AL-FC/AL-FanControl/arduino/bridgehead5V_ino/bridgehead5V_ino.ino

// fancontrol.ino
//
// Intentionally left simple and stupid so that all intelligent code can reside on the host side.

#include <SoftPWM.h>

// pins to which the fans are connected physically
// connector index  0  1  2  3   4   5   6   7
int PINS_PWM[]   = {2, 6}; //, 9, 4, A3, 15, 10, A1};
int PINS_PULSE[] = {3, 7}; //, 8, 5, A2, 14, 16, A0};

void setup() {
  // initialize serial connection
  Serial.begin(9600);
  
  // init pwm
  SoftPWMBegin();
  for (int i = 0; i < 2; i++) {      
    pinMode(PINS_PULSE[i], INPUT);
    digitalWrite(PINS_PULSE[i],HIGH);
    
    SoftPWMSetFadeTime(PINS_PWM[i], 0, 0);
    SoftPWMSet(PINS_PWM[i], 0);
  }
}

void loop() {
  // get message from serial console
  String message = "";
  while (Serial.available())
    message.concat((char) Serial.read());
  if (message == "")
    return;

  // iterate fans, collect pulse durations
  String pulseDurations = ":";
  for (int i = 0; i < 2; i++) {
    // parse value left of a ';' 
    int value = message.substring(0, message.indexOf(';')).toInt();
    
    SoftPWMSet(PINS_PWM[i], value);
    
    // strip part left of a ';' from message
    message = message.substring(message.indexOf(';') + 1);

    // respond with pulse durations
    pulseDurations = pulseDurations + String(pulseIn(PINS_PULSE[i], LOW)) + ";";
    
    // if there is no further ';' in the message, parse and set the rest of it
    if (message.indexOf(';') == -1)
      SoftPWMSet(PINS_PWM[i], message.toInt());
  }
  Serial.println(pulseDurations);
}
