AL-FC/AL-FanControl/python/fancontrol/learn.py

'''
Learns the correlations between the fans and the temps.
'''
from __future__ import (absolute_import, division, print_function,
                        unicode_literals)


def main():
    '''
    Put system under load and determine minimum viable fan speeds.
    Log fan speeds and temperatures, calculate correlations.
    '''
    pass
