AL-FC/AL-FanControl/arduino/blink_isr/sketch_jan23d/sketch_jan23d.ino

/* Arduino 101: timer and interrupts
   1: Timer1 compare match interrupt example 
   more infos: http://www.letmakerobots.com/node/28278
   created by RobotFreak 
*/

#define ledPin 17

void setup()
{
  pinMode(ledPin, OUTPUT);
  
  // initialize timer1 
  noInterrupts();           // disable all interrupts
  TCCR1A = 0;
  TCCR1B = 0;
  TCNT1  = 0;

  OCR1A = 31250;            // compare match register 16MHz/256/2Hz
  TCCR1B |= (1 << WGM12);   // CTC mode
  TCCR1B |= (1 << CS12);    // 256 prescaler 
  TIMSK1 |= (1 << OCIE1A);  // enable timer compare interrupt
  interrupts();             // enable all interrupts
}

ISR(TIMER1_COMPA_vect)          // timer compare interrupt service routine
{
  digitalWrite(ledPin, digitalRead(ledPin) ^ 1);   // toggle LED pin
}

void loop()
{
  // your program here...
}
